brenocq/2DPenter/Images/RealBackLeft.jpg

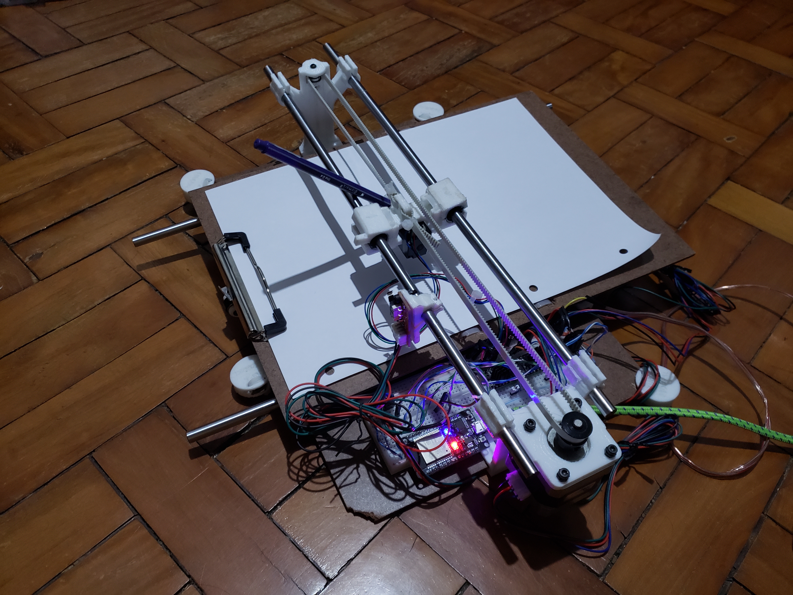
Images/RealBackLeft.jpg
