brenocq/2DPenter/Images/RealFrontLeft.jpg

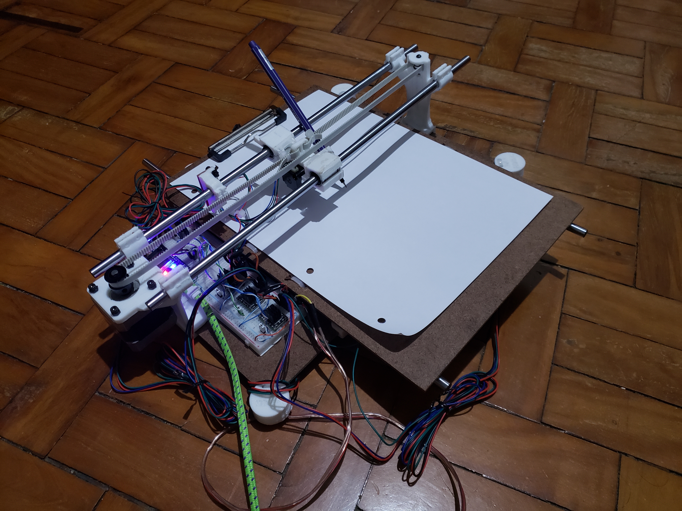
Images/RealFrontLeft.jpg
