brenocq/2DPenter/3Dmodels/Nema8Motor.SLDPRT

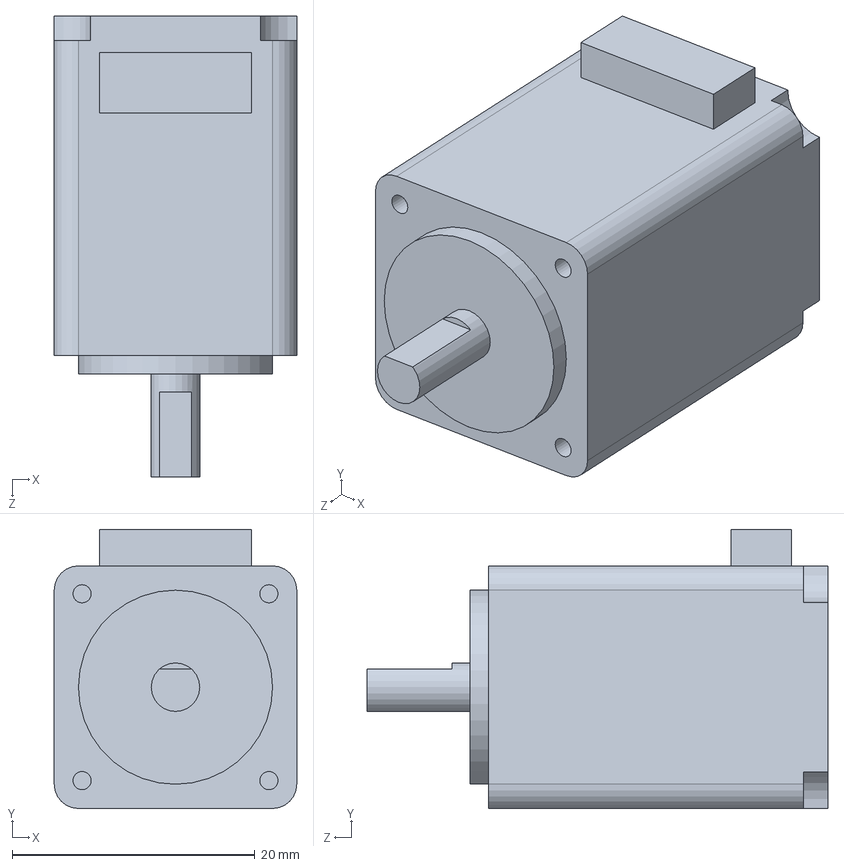
[picture p33: CAD file, 2019-06-20]
3Dmodels/Nema8Motor.SLDPRT
20.0 x 23.0 x 38.0 mm
