brenocq/2DPenter/3Dmodels/F623ZZ Flange.SLDPRT

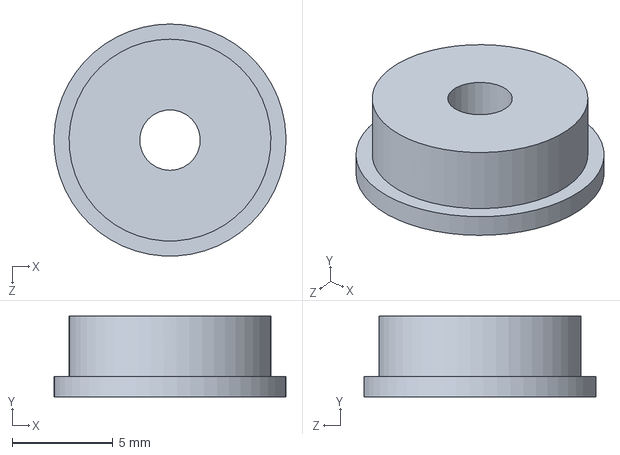
[picture p34: CAD file, 2019-06-20]
3Dmodels/F623ZZ Flange.SLDPRT
11.5 x 4.00 x 11.5 mm
