brenocq/2DPenter/3Dmodels/bed.SLDPRT

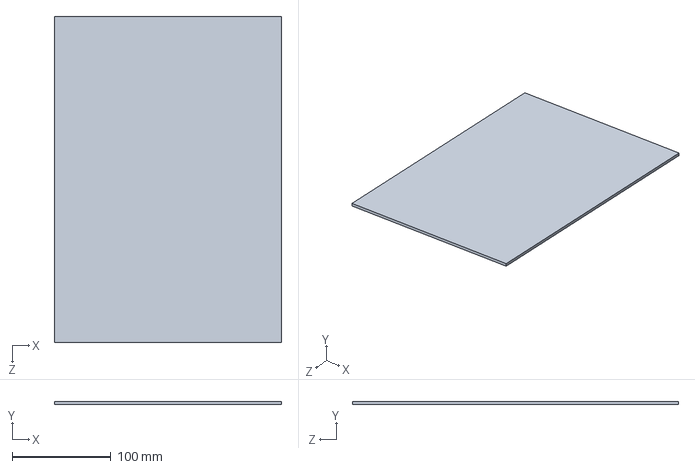
[picture p35: CAD file, 2019-06-20]
3Dmodels/bed.SLDPRT
230.0 x 3.50 x 330.0 mm
