brenocq/2DPenter/3Dmodels/Rolamento LM8UU.SLDPRT

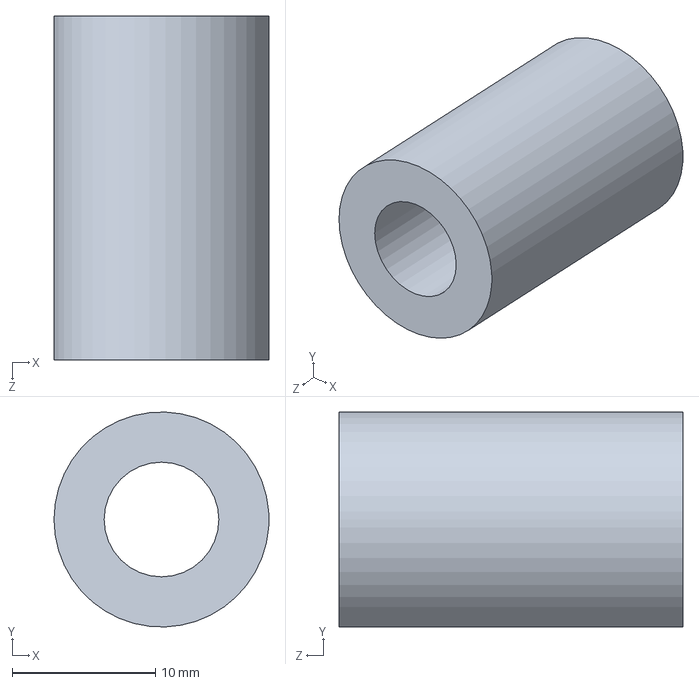
[picture p36: CAD file, 2019-06-20]
3Dmodels/Rolamento LM8UU.SLDPRT
15.0 x 15.0 x 24.0 mm
