brenocq/2DPenter/3Dmodels/SupXMotor.SLDPRT

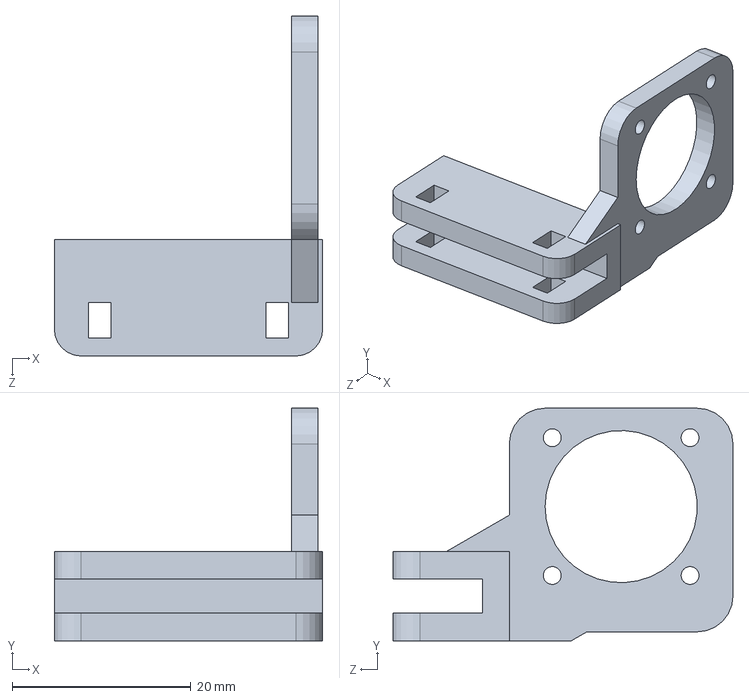
[picture p37: CAD file, 2019-06-20]
3Dmodels/SupXMotor.SLDPRT
30.0 x 26.0 x 38.0 mm
