brenocq/2DPenter/3Dmodels/FixBeltX.SLDPRT

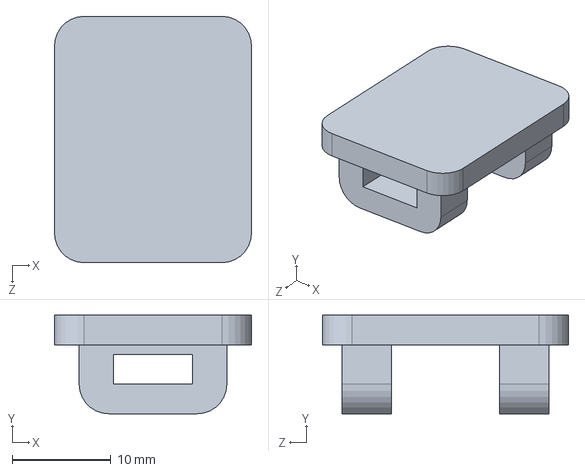
[picture p38: CAD file, 2019-06-20]
3Dmodels/FixBeltX.SLDPRT
20.0 x 10.0 x 25.0 mm
