brenocq/2DPenter/3Dmodels/EndStop.SLDPRT

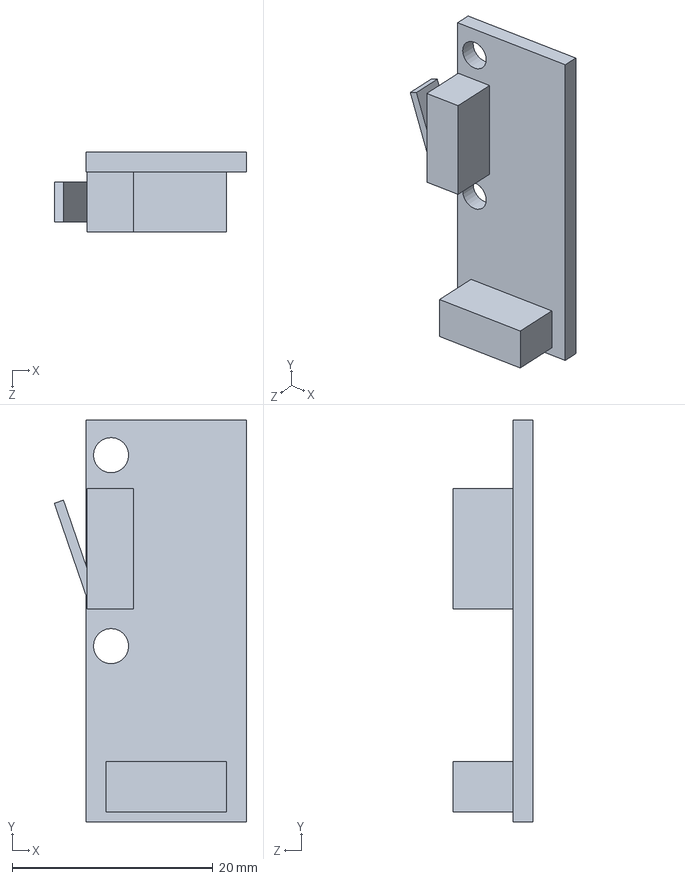
[picture p39: CAD file, 2019-06-20]
3Dmodels/EndStop.SLDPRT
19.2 x 40.0 x 8.00 mm
