brenocq/2DPenter/3Dmodels/Pen.SLDPRT

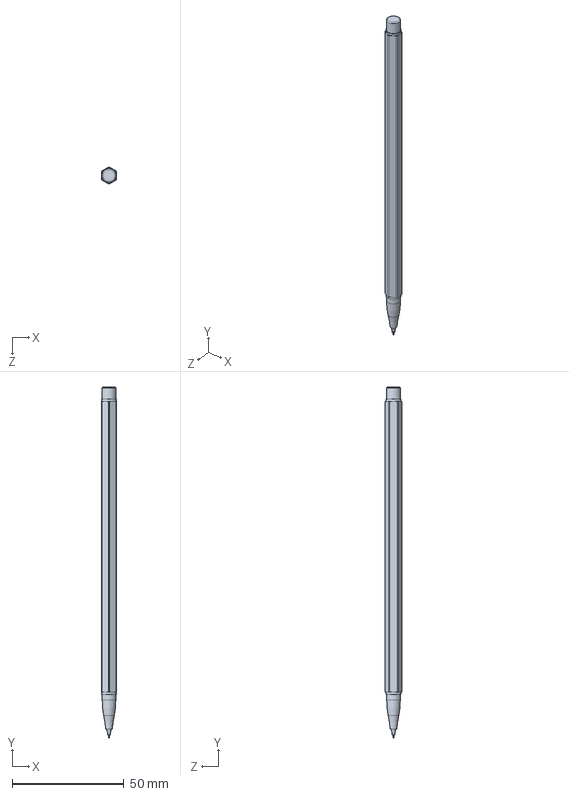
[picture p40: CAD file, 2019-06-20]
3Dmodels/Pen.SLDPRT
6.70 x 156.9 x 7.54 mm
