brenocq/2DPenter/3Dmodels/SupXPulley.SLDPRT

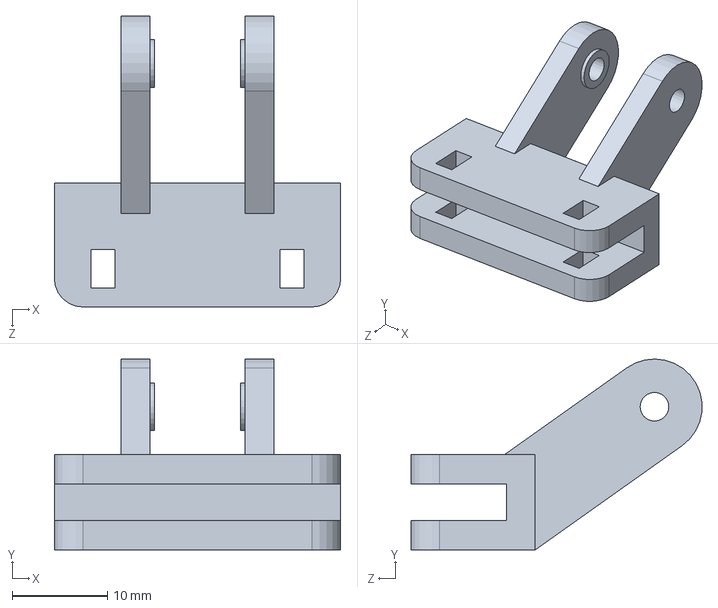
[picture p41: CAD file, 2019-06-20]
3Dmodels/SupXPulley.SLDPRT
30.0 x 20.0 x 30.5 mm
