brenocq/2DPenter/3Dmodels/ESP32.SLDPRT

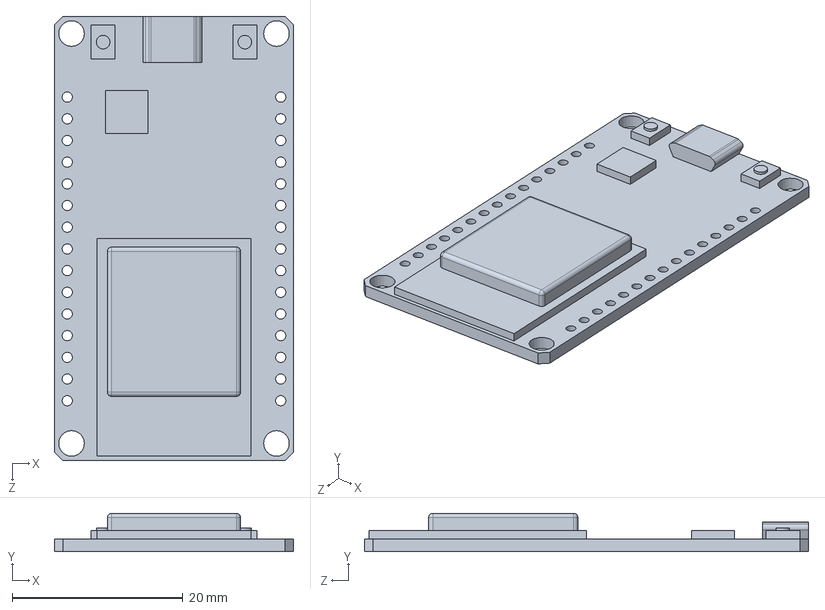
[picture p42: CAD file, 2019-06-20]
3Dmodels/ESP32.SLDPRT
28.0 x 4.50 x 52.0 mm
