brenocq/2DPenter/3Dmodels/Car.SLDPRT

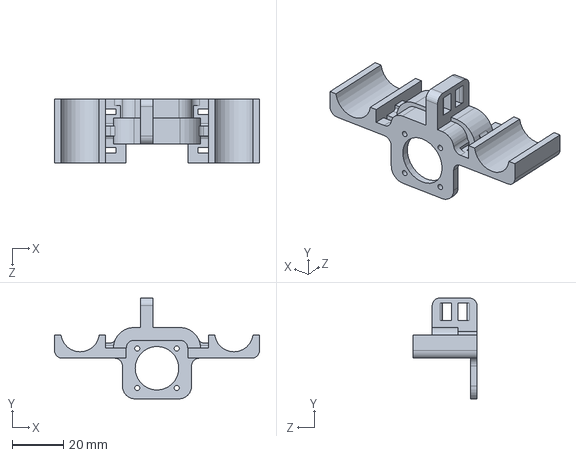
[picture p43: CAD file, 2019-06-20]
3Dmodels/Car.SLDPRT
80.0 x 39.4 x 25.0 mm
