brenocq/2DPenter/3Dmodels/Barra lisa 8x400.SLDPRT

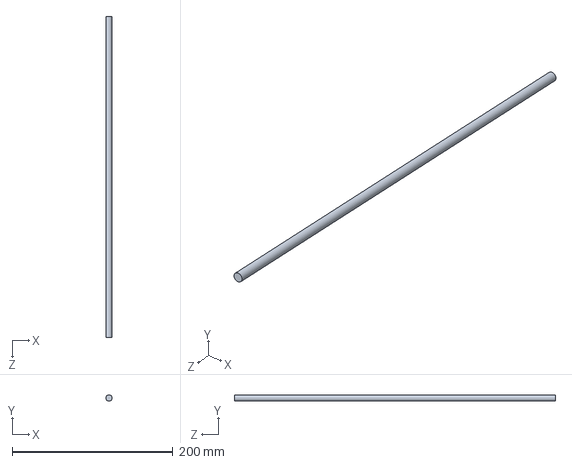
[picture p44: CAD file, 2019-06-20]
3Dmodels/Barra lisa 8x400.SLDPRT
8.00 x 8.00 x 400.0 mm
