brenocq/2DPenter/3Dmodels/SupYPulley.SLDPRT

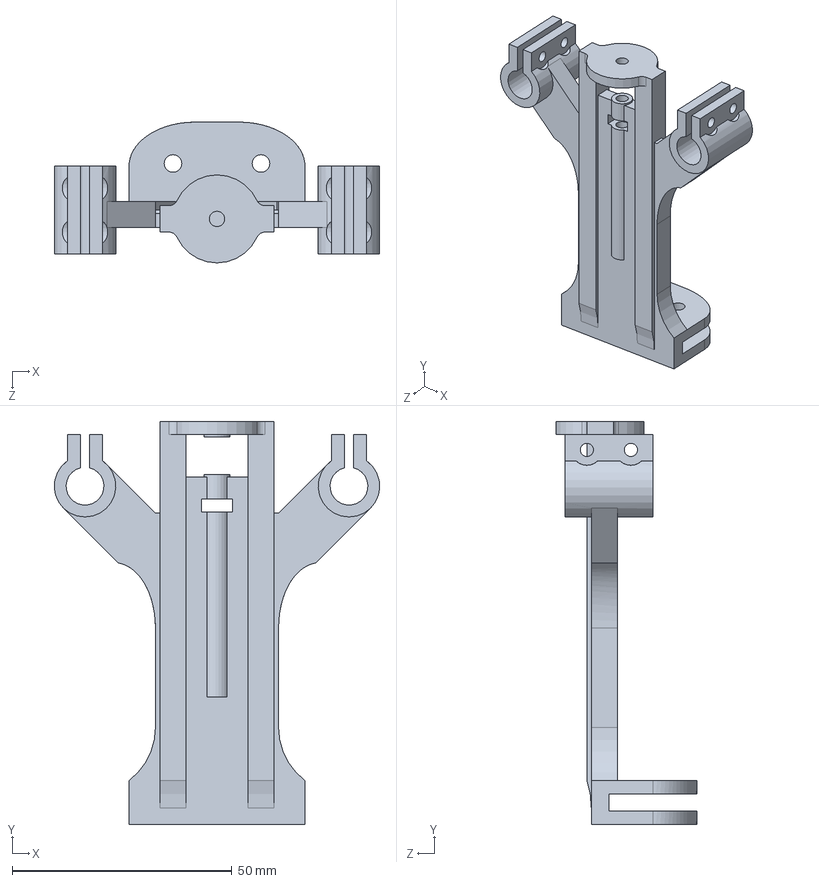
[picture p45: CAD file, 2019-06-20]
3Dmodels/SupYPulley.SLDPRT
74.0 x 91.6 x 32.0 mm
